sb2cl/Heater_TS/matlab/2_ValidacionModelo/112.png

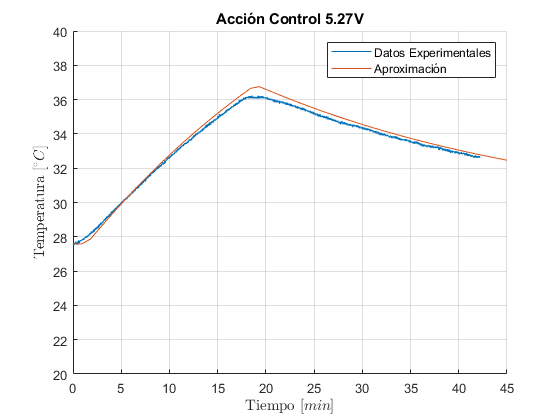
matlab/2_ValidacionModelo/112.png
