sb2cl/Heater_TS/arduino/Heater_Task/Debugger.cpp

/*
 * Copyright (C) 2020 Fernando Nóbel Santos Navarro 
 *
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
 * You should have received a copy of the GNU General Public License
 * along with this program.  If not, see <https://www.gnu.org/licenses/>.
 */

#include "Debugger.h" 

/**
 * @brief: Constructor of Debugger.
 *
 */
Debugger::Debugger()
  : Task()
{
  Serial.begin(9600);
}

/**
 * @brief: The Debugger is executed when there is serial data.
 *
 * @param: uint64_t now Current time in 100 nanoseconds.
 *
 * @return: bool 
 */
bool Debugger::canRun(uint64_t now)
{
  return Serial.available() > 0;
}

/**
 * @brief: The Debugger echoes the data recived form serial.
 *
 * @param: uint64_t now Current time in 100 nanoseconds.
 *
 * @return: void 
 */
void Debugger::run(uint64_t now)
{
  uint16_t byteCount = 0;

  Serial.println("-----------------");
  Serial.println("Input Received...");
  Serial.println("-----------------");
  while (Serial.available() > 0) {
    int byte = Serial.read();
    Serial.print("'") ;
    Serial.print(char(byte));
    Serial.print("' = ");
    Serial.print(byte, DEC);
    Serial.println(" ");
    if (byte == '\r') {
      Serial.print('\n', DEC);
    }

    byteCount++;
  }

  Serial.println("-----------------");
  Serial.print("Bytes Received: "); Serial.println(String(byteCount));
  Serial.println("-----------------");

}

/**
 * @brief: Provies basic debug info from other tasks.
 *
 * @param: String debugMsg Debug message to send.
 *
 * @return: void 
 */
void Debugger::debugWrite(String debugMsg)
{
  Serial.println(debugMsg);
}
